upenn-embedded/final-project-s25-t-t-slots-sense-the-win/docs/HRS_02_05.jpeg

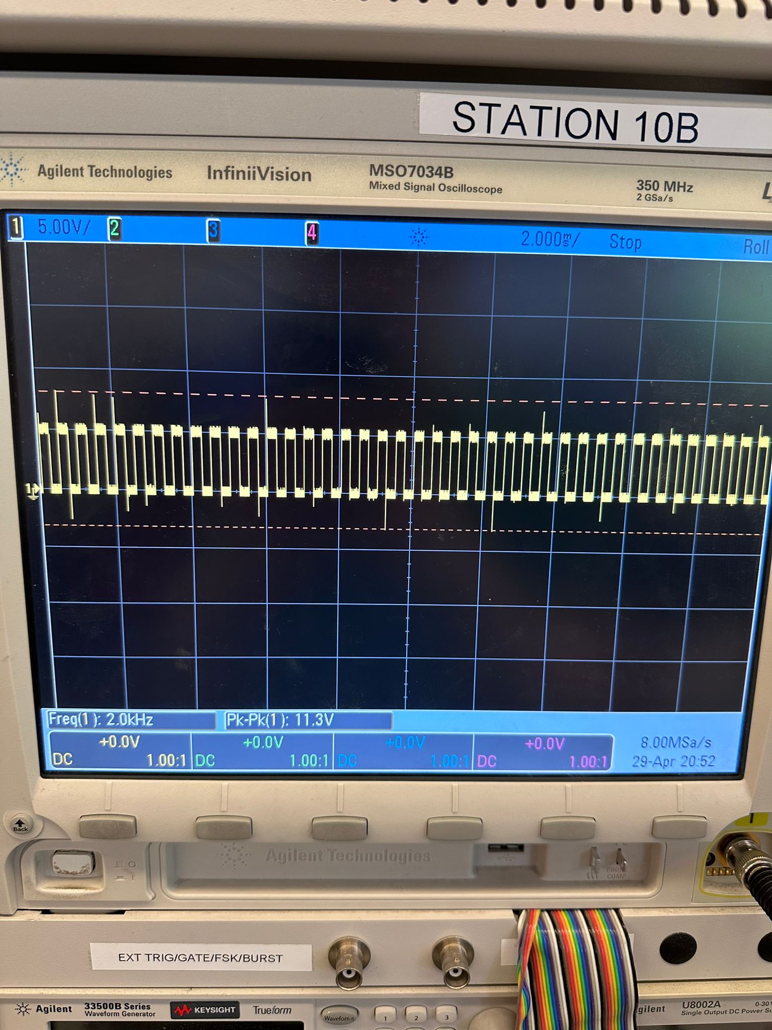
docs/HRS_02_05.jpeg
